paroda/kekdaboard/board/board-left/board-left.kicad_sch

## KiCad design board/board-left/board-left.kicad_sch (2023-03-22)

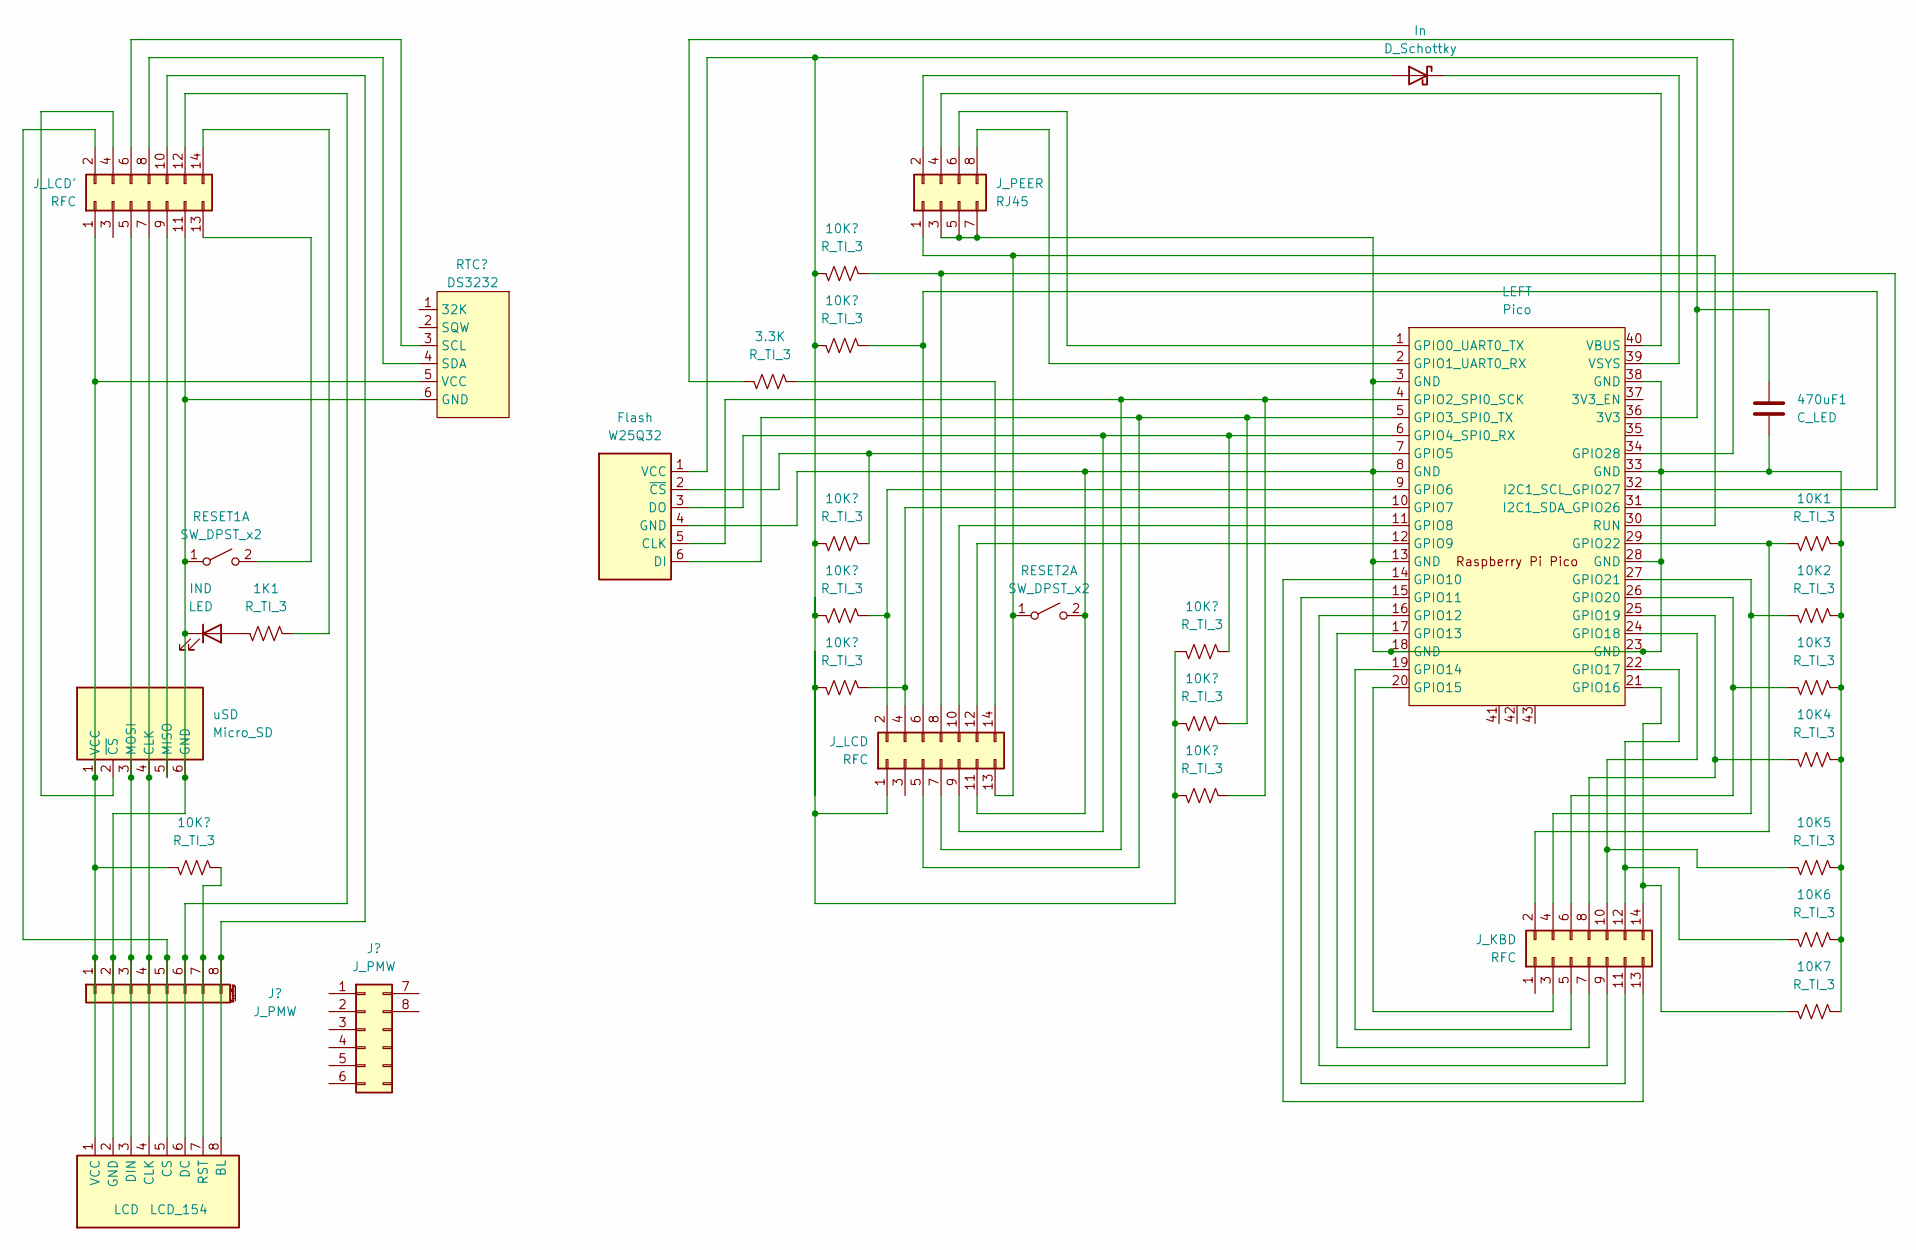
[picture p7: schematic board-left.kicad_sch]

Parts:
1K1, 3.3K, 10K1, 10K2, 10K3, 10K4, 10K5, 10K6, 10K7: R_TI_3; R_Axial_DIN0204_L3.6mm_D1.6mm_P2.54mm_Vertical
470uF1: C_LED
Flash: W25Q32; SOIC-8_5.23x5.23mm_P1.27mm
IND: LED
In: D_Schottky
J_KBD: RFC; PinSocket_2x07_P2.54mm_Vertical
J_LCD: RFC; PinSocket_2x07_P2.54mm_Vertical
J_LCD': RFC; PinSocket_2x07_P2.54mm_Vertical
J_PEER: RJ45; RJ45_Amphenol_54602-x08_Horizontal
LCD: LCD_154; SOIC-8_5.23x5.23mm_P1.27mm
LEFT: Pico; RPi_Pico_SMD_TH
RESET1, RESET2: SW_DPST_x2
uSD: Micro_SD; SOIC-8_5.23x5.23mm_P1.27mm

Connections:
unnamed: 1K1.1, J_LCD'.14
unnamed: 1K1.2, IND.2 (A)
unnamed: 3.3K.1, J_LCD.14
unnamed: 3.3K.2, LEFT.34 (GPIO28)
unnamed: 10K1.1, 10K2.1, 10K3.1, 10K4.1, 10K5.1, 10K6.1, 10K7.1, 470uF1.2, Flash.4 (GND), J_LCD.11, J_PEER.3, J_PEER.5, J_PEER.7, LEFT.3 (GND), LEFT.8 (GND), LEFT.13 (GND), LEFT.18 (GND), LEFT.23 (GND), LEFT.28 (GND), LEFT.33 (GND), LEFT.38 (GND), RESET2.2 (B)
unnamed: 10K1.2, J_KBD.2, LEFT.29 (GPIO22)
unnamed: 10K2.2, J_KBD.4, LEFT.27 (GPIO21)
unnamed: 10K3.2, J_KBD.6, LEFT.26 (GPIO20)
unnamed: 10K4.2, J_KBD.8, LEFT.25 (GPIO19)
unnamed: 10K5.2, J_KBD.10, LEFT.24 (GPIO18)
unnamed: 10K6.2, J_KBD.12, LEFT.22 (GPIO17)
unnamed: 10K7.2, J_KBD.14, LEFT.21 (GPIO16)
unnamed: 470uF1.1, Flash.1 (VCC), J_LCD.1, LEFT.36 (3V3)
unnamed: Flash.2 (~CS), LEFT.7 (GPIO5)
unnamed: Flash.3 (DO), J_LCD.9, LEFT.6 (GPIO4_SPI0_RX)
unnamed: Flash.5 (CLK), J_LCD.7, LEFT.4 (GPIO2_SPI0_SCK)
unnamed: Flash.6 (DI), J_LCD.5, LEFT.5 (GPIO3_SPI0_TX)
unnamed: IND.1 (K), J_LCD'.11, LCD.2 (GND), RESET1.1 (A), uSD.6 (GND)
unnamed: In.1 (K), LEFT.39 (VSYS)
unnamed: In.2 (A), J_PEER.2
unnamed: J_KBD.3, LEFT.20 (GPIO15)
unnamed: J_KBD.5, LEFT.19 (GPIO14)
unnamed: J_KBD.7, LEFT.17 (GPIO13)
unnamed: J_KBD.9, LEFT.16 (GPIO12)
unnamed: J_KBD.11, LEFT.15 (GPIO11)
unnamed: J_KBD.13, LEFT.14 (GPIO10)
unnamed: J_LCD'.1, LCD.1 (VCC), uSD.1 (VCC)
unnamed: J_LCD'.2, LCD.5 (CS)
unnamed: J_LCD'.4, uSD.2 (~CS)
unnamed: J_LCD'.5, LCD.3 (DIN), uSD.3 (MOSI)
unnamed: J_LCD'.7, LCD.4 (CLK), uSD.4 (CLK)
unnamed: J_LCD'.9, uSD.5 (MISO)
unnamed: J_LCD'.10, LCD.8 (BL)
unnamed: J_LCD'.12, LCD.6 (DC)
unnamed: J_LCD'.13, RESET1.2 (B)
unnamed: J_LCD.2, LEFT.9 (GPIO6)
unnamed: J_LCD.4, LEFT.10 (GPIO7)
unnamed: J_LCD.6, LEFT.32 (I2C1_SCL_GPIO27)
unnamed: J_LCD.8, LEFT.31 (I2C1_SDA_GPIO26)
unnamed: J_LCD.10, LEFT.11 (GPIO8)
unnamed: J_LCD.12, LEFT.12 (GPIO9)
unnamed: J_LCD.13, J_PEER.1, LEFT.30 (RUN), RESET2.1 (A)
unnamed: J_PEER.4, LEFT.40 (VBUS)
unnamed: J_PEER.6, LEFT.1 (GPIO0_UART0_TX)
unnamed: J_PEER.8, LEFT.2 (GPIO1_UART0_RX)
