paroda/kekdaboard/picow/hello_bt/gatt_streamer_server.c

/*
 * Copyright (C) 2014 BlueKitchen GmbH
 *
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
 * 1. Redistributions of source code must retain the above copyright
 *    notice, this list of conditions and the following disclaimer.
 * 2. Redistributions in binary form must reproduce the above copyright
 *    notice, this list of conditions and the following disclaimer in the
 *    documentation and/or other materials provided with the distribution.
 * 3. Neither the name of the copyright holders nor the names of
 *    contributors may be used to endorse or promote products derived
 *    from this software without specific prior written permission.
 * 4. Any redistribution, use, or modification is done solely for
 *    personal benefit and not for any commercial purpose or for
 *    monetary gain.
 *
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
 * Please inquire about commercial licensing options at
 * contact@bluekitchen-gmbh.com
 *
 */

#define BTSTACK_FILE__ "gatt_streamer_server.c"

// *****************************************************************************
/* EXAMPLE_START(gatt_streamer_server): Performance - Stream Data over GATT (Server)
 *
 * @text All newer operating systems provide GATT Client functionality.
 * This example shows how to get a maximal throughput via BLE:
 * - send whenever possible,
 * - use the max ATT MTU.
 *
 * @text In theory, we should also update the connection parameters, but we already get
 * a connection interval of 30 ms and there's no public way to use a shorter
 * interval with iOS (if we're not implementing an HID device).
 *
 * @text Note: To start the streaming, run the example.
 * On remote device use some GATT Explorer, e.g. LightBlue, BLExplr to enable notifications.
 */
// *****************************************************************************

#include <inttypes.h>
#include <stdint.h>
#include <stdio.h>
#include <stdlib.h>
#include <string.h>

#include "btstack.h"
#include "pico/cyw43_arch.h"
#include "pico/btstack_cyw43.h"
#include "pico/stdlib.h"

// le_streamer.gatt contains the declaration of the provided GATT Services + Characteristics
// le_streamer.h    contains the binary representation of le_streamer.gatt
// it is generated by the build system by calling: $BTSTACK_ROOT/tool/compile_gatt.py le_streamer.gatt le_streamer.h
// it needs to be regenerated when the GATT Database declared in le_streamer.gatt file is modified
#include "gatt_streamer_server.h"

#define REPORT_INTERVAL_MS 3000
#define MAX_NR_CONNECTIONS 3


static void  hci_packet_handler (uint8_t packet_type, uint16_t channel, uint8_t *packet, uint16_t size);
static void  att_packet_handler (uint8_t packet_type, uint16_t channel, uint8_t *packet, uint16_t size);
static int   att_write_callback(hci_con_handle_t con_handle, uint16_t att_handle, uint16_t transaction_mode, uint16_t offset, uint8_t *buffer, uint16_t buffer_size);
static void  streamer(void);

#define APP_AD_FLAGS 0x06

const uint8_t adv_data[] = {
    // Flags general discoverable
    0x02, BLUETOOTH_DATA_TYPE_FLAGS, APP_AD_FLAGS,
    // Name
    0x0c, BLUETOOTH_DATA_TYPE_COMPLETE_LOCAL_NAME, 'L', 'E', ' ', 'S', 't', 'r', 'e', 'a', 'm', 'e', 'r',
    // Incomplete List of 16-bit Service Class UUIDs -- FF10 - only valid for testing!
    0x03, BLUETOOTH_DATA_TYPE_INCOMPLETE_LIST_OF_16_BIT_SERVICE_CLASS_UUIDS, 0x10, 0xff,
};
const uint8_t adv_data_len = sizeof(adv_data);

static btstack_packet_callback_registration_t hci_event_callback_registration;

// support for multiple clients
typedef struct {
    char name;
    int le_notification_enabled;
    uint16_t value_handle;
    hci_con_handle_t connection_handle;
    int  counter;
    char test_data[200];
    int  test_data_len;
    uint32_t test_data_sent_count;
    uint32_t test_data_sent;
    uint32_t test_data_start;
} le_streamer_connection_t;
static le_streamer_connection_t le_streamer_connections[MAX_NR_CONNECTIONS];

// round robin sending
static int connection_index;

static void init_connections(void){
    // track connections
    int i;
    for (i=0;i<MAX_NR_CONNECTIONS;i++){
        le_streamer_connections[i].connection_handle = HCI_CON_HANDLE_INVALID;
        le_streamer_connections[i].name = 'A' + i;
    }
}

static le_streamer_connection_t * connection_for_conn_handle(hci_con_handle_t conn_handle){
    int i;
    for (i=0;i<MAX_NR_CONNECTIONS;i++){
        if (le_streamer_connections[i].connection_handle == conn_handle) return &le_streamer_connections[i];
    }
    return NULL;
}

static void next_connection_index(void){
    connection_index++;
    if (connection_index == MAX_NR_CONNECTIONS){
        connection_index = 0;
    }
}

/* @section Main Application Setup
 *
 * @text Listing MainConfiguration shows main application code.
 * It initializes L2CAP, the Security Manager, and configures the ATT Server with the pre-compiled
 * ATT Database generated from $le_streamer.gatt$. Finally, it configures the advertisements
 * and boots the Bluetooth stack.
 */

/* LISTING_START(MainConfiguration): Init L2CAP, SM, ATT Server, and enable advertisements */

static void le_streamer_setup(void){

    l2cap_init();

    // setup SM: Display only
    sm_init();

    // setup ATT server
    att_server_init(profile_data, NULL, att_write_callback);

    // register for HCI events
    hci_event_callback_registration.callback = &hci_packet_handler;
    hci_add_event_handler(&hci_event_callback_registration);

    // register for ATT events
    att_server_register_packet_handler(att_packet_handler);

    // setup advertisements
    uint16_t adv_int_min = 0x0030;
    uint16_t adv_int_max = 0x0030;
    uint8_t adv_type = 0;
    bd_addr_t null_addr;
    memset(null_addr, 0, 6);
    gap_advertisements_set_params(adv_int_min, adv_int_max, adv_type, 0, null_addr, 0x07, 0x00);
    gap_advertisements_set_data(adv_data_len, (uint8_t*) adv_data);
    gap_advertisements_enable(1);

    // init client state
    init_connections();
}
/* LISTING_END */

/*
 * @section Track throughput
 * @text We calculate the throughput by setting a start time and measuring the amount of
 * data sent. After a configurable REPORT_INTERVAL_MS, we print the throughput in kB/s
 * and reset the counter and start time.
 */

/* LISTING_START(tracking): Tracking throughput */

static void test_reset(le_streamer_connection_t * context){
    context->test_data_start = btstack_run_loop_get_time_ms();
    context->test_data_sent = 0;
    context->test_data_sent_count = 0;
}

static void test_track_sent(le_streamer_connection_t * context, int bytes_sent){
    context->test_data_sent += bytes_sent;
    context->test_data_sent_count++;

    // evaluate
    uint32_t now = btstack_run_loop_get_time_ms();
    uint32_t time_passed = now - context->test_data_start;
    if (time_passed < REPORT_INTERVAL_MS) return;
    // print speed
    int bytes_per_second = context->test_data_sent * 1000 / time_passed;
    int count_per_second = context->test_data_sent_count * 1000 / time_passed;
    printf("%c: %"PRIu32" bytes sent-> %u.%03u kB/s %u times/sec\n", context->name, context->test_data_sent, bytes_per_second / 1000, bytes_per_second % 1000, count_per_second);

    // restart
    context->test_data_start = now;
    context->test_data_sent  = 0;
    context->test_data_sent_count  = 0;
}
/* LISTING_END(tracking): Tracking throughput */

/*
 * @section HCI Packet Handler
 *
 * @text The packet handler is used track incoming connections and to stop notifications on disconnect
 * It is also a good place to request the connection parameter update as indicated
 * in the commented code block.
 */

/* LISTING_START(hciPacketHandler): Packet Handler */
static void hci_packet_handler (uint8_t packet_type, uint16_t channel, uint8_t *packet, uint16_t size){
    UNUSED(channel);
    UNUSED(size);

    if (packet_type != HCI_EVENT_PACKET) return;

    uint16_t conn_interval;
    hci_con_handle_t con_handle;

    switch (hci_event_packet_get_type(packet)) {
    case BTSTACK_EVENT_STATE:
        // BTstack activated, get started
        if (btstack_event_state_get_state(packet) == HCI_STATE_WORKING) {
            printf("To start the streaming, please run the le_streamer_client example on other device, or use some GATT Explorer, e.g. LightBlue, BLExplr.\n");
        }
        break;
    case HCI_EVENT_DISCONNECTION_COMPLETE:
        con_handle = hci_event_disconnection_complete_get_connection_handle(packet);
        printf("- LE Connection 0x%04x: disconnect, reason %02x\n", con_handle, hci_event_disconnection_complete_get_reason(packet));
        break;
    case HCI_EVENT_LE_META:
        switch (hci_event_le_meta_get_subevent_code(packet)) {
        case HCI_SUBEVENT_LE_CONNECTION_COMPLETE:
            // print connection parameters (without using float operations)
            con_handle    = hci_subevent_le_connection_complete_get_connection_handle(packet);
            conn_interval = hci_subevent_le_connection_complete_get_conn_interval(packet);
            printf("- LE Connection 0x%04x: connected - connection interval %u.%02u ms, latency %u\n", con_handle, conn_interval * 125 / 100,
                   25 * (conn_interval & 3), hci_subevent_le_connection_complete_get_conn_latency(packet));

            // request min con interval 15 ms for iOS 11+
            //printf("- LE Connection 0x%04x: request 15 ms connection interval\n", con_handle);
            //gap_request_connection_parameter_update(con_handle, 12, 12, 4, 0x0048);
            break;
        case HCI_SUBEVENT_LE_CONNECTION_UPDATE_COMPLETE:
            // print connection parameters (without using float operations)
            con_handle    = hci_subevent_le_connection_update_complete_get_connection_handle(packet);
            conn_interval = hci_subevent_le_connection_update_complete_get_conn_interval(packet);
            printf("- LE Connection 0x%04x: connection update - connection interval %u.%02u ms, latency %u\n", con_handle, conn_interval * 125 / 100,
                   25 * (conn_interval & 3), hci_subevent_le_connection_update_complete_get_conn_latency(packet));
            break;
        case HCI_SUBEVENT_LE_DATA_LENGTH_CHANGE:
            con_handle = hci_subevent_le_data_length_change_get_connection_handle(packet);
            printf("- LE Connection 0x%04x: data length change - max %u bytes per packet\n", con_handle,
                   hci_subevent_le_data_length_change_get_max_tx_octets(packet));
            break;
        default:
            break;
        }
        break;

    default:
        break;
    }
}

/* LISTING_END */

/*
 * @section ATT Packet Handler
 *
 * @text The packet handler is used to track the ATT MTU Exchange and trigger ATT send
 */

/* LISTING_START(attPacketHandler): Packet Handler */
static void att_packet_handler (uint8_t packet_type, uint16_t channel, uint8_t *packet, uint16_t size){
    UNUSED(channel);
    UNUSED(size);

    int mtu;
    le_streamer_connection_t * context;
    switch (packet_type) {
    case HCI_EVENT_PACKET:
        switch (hci_event_packet_get_type(packet)) {
        case ATT_EVENT_CONNECTED:
            // setup new
            context = connection_for_conn_handle(HCI_CON_HANDLE_INVALID);
            if (!context) break;
            context->counter = 'A';
            context->connection_handle = att_event_connected_get_handle(packet);
            context->test_data_len = btstack_min(att_server_get_mtu(context->connection_handle) - 3, sizeof(context->test_data));
            printf("%c: ATT connected, handle 0x%04x, test data len %u\n", context->name, context->connection_handle, context->test_data_len);
            break;
        case ATT_EVENT_MTU_EXCHANGE_COMPLETE:
            mtu = att_event_mtu_exchange_complete_get_MTU(packet) - 3;
            context = connection_for_conn_handle(att_event_mtu_exchange_complete_get_handle(packet));
            if (!context) break;
            context->test_data_len = btstack_min(mtu - 3, sizeof(context->test_data));
            printf("%c: ATT MTU = %u => use test data of len %u\n", context->name, mtu, context->test_data_len);
            break;
        case ATT_EVENT_CAN_SEND_NOW:
            streamer();
            break;
        case ATT_EVENT_DISCONNECTED:
            context = connection_for_conn_handle(att_event_disconnected_get_handle(packet));
            if (!context) break;
            // free connection
            printf("%c: ATT disconnected, handle 0x%04x\n", context->name, context->connection_handle);
            context->le_notification_enabled = 0;
            context->connection_handle = HCI_CON_HANDLE_INVALID;
            break;
        default:
            break;
        }
        break;
    default:
        break;
    }
}
/* LISTING_END */

/*
 * @section Streamer
 *
 * @text The streamer function checks if notifications are enabled and if a notification can be sent now.
 * It creates some test data - a single letter that gets increased every time - and tracks the data sent.
 */

/* LISTING_START(streamer): Streaming code */
static void streamer(void){

    // find next active streaming connection
    int old_connection_index = connection_index;
    while (1){
        // active found?
        if ((le_streamer_connections[connection_index].connection_handle != HCI_CON_HANDLE_INVALID) &&
            (le_streamer_connections[connection_index].le_notification_enabled)) break;

        // check next
        next_connection_index();

        // none found
        if (connection_index == old_connection_index) return;
    }

    le_streamer_connection_t * context = &le_streamer_connections[connection_index];

    // create test data
    context->counter++;
    if (context->counter > 'Z') context->counter = 'A';
    memset(context->test_data, context->counter, context->test_data_len);

    // send
    att_server_notify(context->connection_handle, context->value_handle, (uint8_t*) context->test_data, context->test_data_len);

    // track
    test_track_sent(context, context->test_data_len);

    // request next send event
    att_server_request_can_send_now_event(context->connection_handle);

    // check next
    next_connection_index();
}
/* LISTING_END */

/*
 * @section ATT Write
 *
 * @text The only valid ATT write in this example is to the Client Characteristic Configuration, which configures notification
 * and indication. If the ATT handle matches the client configuration handle, the new configuration value is stored.
 * If notifications get enabled, an ATT_EVENT_CAN_SEND_NOW is requested. See Listing attWrite.
 */

/* LISTING_START(attWrite): ATT Write */
static int att_write_callback(hci_con_handle_t con_handle, uint16_t att_handle, uint16_t transaction_mode, uint16_t offset, uint8_t *buffer, uint16_t buffer_size){
    UNUSED(offset);

    // printf("att_write_callback att_handle 0x%04x, transaction mode %u\n", att_handle, transaction_mode);
    if (transaction_mode != ATT_TRANSACTION_MODE_NONE) return 0;
    le_streamer_connection_t * context = connection_for_conn_handle(con_handle);
    switch(att_handle){
    case ATT_CHARACTERISTIC_0000FF11_0000_1000_8000_00805F9B34FB_01_CLIENT_CONFIGURATION_HANDLE:
    case ATT_CHARACTERISTIC_0000FF12_0000_1000_8000_00805F9B34FB_01_CLIENT_CONFIGURATION_HANDLE:
        context->le_notification_enabled = little_endian_read_16(buffer, 0) == GATT_CLIENT_CHARACTERISTICS_CONFIGURATION_NOTIFICATION;
        printf("%c: Notifications enabled %u\n", context->name, context->le_notification_enabled);
        if (context->le_notification_enabled){
            switch (att_handle){
            case ATT_CHARACTERISTIC_0000FF11_0000_1000_8000_00805F9B34FB_01_CLIENT_CONFIGURATION_HANDLE:
                context->value_handle = ATT_CHARACTERISTIC_0000FF11_0000_1000_8000_00805F9B34FB_01_VALUE_HANDLE;
                break;
            case ATT_CHARACTERISTIC_0000FF12_0000_1000_8000_00805F9B34FB_01_CLIENT_CONFIGURATION_HANDLE:
                context->value_handle = ATT_CHARACTERISTIC_0000FF12_0000_1000_8000_00805F9B34FB_01_VALUE_HANDLE;
                break;
            default:
                break;
            }
            att_server_request_can_send_now_event(context->connection_handle);
        }
        test_reset(context);
        break;
    case ATT_CHARACTERISTIC_0000FF11_0000_1000_8000_00805F9B34FB_01_VALUE_HANDLE:
    case ATT_CHARACTERISTIC_0000FF12_0000_1000_8000_00805F9B34FB_01_VALUE_HANDLE:
        test_track_sent(context, buffer_size);
        break;
    default:
        printf("Write to 0x%04x, len %u\n", att_handle, buffer_size);
        break;
    }
    return 0;
}
/* LISTING_END */

int btstack_main(void);
int btstack_main(void)
{
    le_streamer_setup();

    // turn on!
    hci_power_control(HCI_POWER_ON);

    return 0;
}
/* EXAMPLE_END */



int main() {

    stdio_init_all();
    sleep_ms(2000);

    printf("Booting up streamer\n");


    // initialize CYW43 driver architecture (will enable BT if/because CYW43_ENABLE_BLUETOOTH == 1)
    if (cyw43_arch_init()) {
        printf("failed to initialise cyw43_arch\n");
        printf("abort!\n");
        sleep_ms(2000);
    }

    printf("cyw43 inited\n");

    cyw43_arch_gpio_put(CYW43_WL_GPIO_LED_PIN, 1);

    btstack_main();

    // btstack_run_loop_execute is only required when using the 'polling' method (e.g. using pico_cyw43_arch_poll library).
    // btstack_run_loop_execute();

    while(true) {
        cyw43_arch_gpio_put(CYW43_WL_GPIO_LED_PIN, 1);
        sleep_ms(300);
        cyw43_arch_gpio_put(CYW43_WL_GPIO_LED_PIN, 0);
        sleep_ms(300);
    }

    return 0;
}
