paroda/kekdaboard/pico/hello_pwm/hello_pwm.c

/**
 * Copyright (c) 2020 Raspberry Pi (Trading) Ltd.
 *
 * SPDX-License-Identifier: BSD-3-Clause
 */

// Output PWM signals on pins 0 and 1

#include "pico/stdlib.h"
#include "hardware/pwm.h"

int main() {
    /// \tag::setup_pwm[]

    // Tell GPIO 0 and 1 they are allocated to the PWM
    gpio_set_function(0, GPIO_FUNC_PWM);
    gpio_set_function(1, GPIO_FUNC_PWM);

    // Find out which PWM slice is connected to GPIO 0 (it's slice 0)
    // uint slice_num = pwm_gpio_to_slice_num(0);
    uint slice_num = pwm_gpio_to_slice_num(1);

    // 50Hz - 38,0
    // 100Hz - 19,0
    pwm_set_clkdiv_int_frac(slice_num, 2, 0);
    pwm_set_wrap(slice_num, 65535);
    pwm_set_chan_level(slice_num, PWM_CHAN_B, 7*65535/10);
    
    // Set the PWM running
    pwm_set_enabled(slice_num, true);
    /// \end::setup_pwm[]

    // Note we could also use pwm_set_gpio_level(gpio, x) which looks up the
    // correct slice and channel for a given GPIO.
}
