paroda/kekdaboard/pico/kbd/srom_pmw3389.c

#include <pico/platform.h>

#include "srom_pmw3389.h"

// Firmware "ORCA3_ROW_SROMxE8"

const unsigned short firmware_length = 4094;

const unsigned char __in_flash() firmware_data[] = {
0x01, 0xe8, 0xba, 0x26, 0x0b, 0xb2, 0xbe, 0xfe, 0x7e, 0x5f, 0x3c, 0xdb, 0x15, 0xa8, 0xb3,
0xe4, 0x2b, 0xb5, 0xe8, 0x53, 0x07, 0x6d, 0x3b, 0xd1, 0x20, 0xc2, 0x06, 0x6f, 0x3d, 0xd9,
0x11, 0xa0, 0xc2, 0xe7, 0x2d, 0xb9, 0xd1, 0x20, 0xa3, 0xa5, 0xc8, 0xf3, 0x64, 0x4a, 0xf7,
0x4d, 0x18, 0x93, 0xa4, 0xca, 0xf7, 0x6c, 0x5a, 0x36, 0xee, 0x5e, 0x3e, 0xfe, 0x7e, 0x7e,
0x5f, 0x1d, 0x99, 0xb0, 0xc3, 0xe5, 0x29, 0xd3, 0x03, 0x65, 0x48, 0x12, 0x87, 0x6d, 0x58,
0x32, 0xe6, 0x2f, 0xdc, 0x3a, 0xf2, 0x4f, 0xfd, 0x59, 0x11, 0x81, 0x61, 0x21, 0xc0, 0x02,
0x86, 0x8e, 0x7f, 0x5d, 0x38, 0xf2, 0x47, 0x0c, 0x7b, 0x55, 0x28, 0xb3, 0xe4, 0x4a, 0x16,
0xab, 0xbf, 0xdd, 0x38, 0xf2, 0x66, 0x4e, 0xff, 0x5d, 0x19, 0x91, 0xa0, 0xa3, 0xa5, 0xc8,
0x12, 0xa6, 0xaf, 0xdc, 0x3a, 0xd1, 0x41, 0x60, 0x75, 0x58, 0x24, 0x92, 0xd4, 0x72, 0x6c,
0xe0, 0x2f, 0xfd, 0x23, 0x8d, 0x1c, 0x5b, 0xb2, 0x97, 0x36, 0x3d, 0x0b, 0xa2, 0x49, 0xb1,
0x58, 0xf2, 0x1f, 0xc0, 0xcb, 0xf8, 0x41, 0x4f, 0xcd, 0x1e, 0x6b, 0x39, 0xa7, 0x2b, 0xe9,
0x30, 0x16, 0x83, 0xd2, 0x0e, 0x47, 0x8f, 0xe3, 0xb1, 0xdf, 0xa2, 0x15, 0xdb, 0x5d, 0x30,
0xc5, 0x1a, 0xab, 0x31, 0x99, 0xf3, 0xfa, 0xb2, 0x86, 0x69, 0xad, 0x7a, 0xe8, 0xa7, 0x18,
0x6a, 0xcc, 0xc8, 0x65, 0x23, 0x87, 0xa8, 0x5f, 0xf5, 0x21, 0x59, 0x75, 0x09, 0x71, 0x45,
0x55, 0x25, 0x4b, 0xda, 0xa1, 0xc3, 0xf7, 0x41, 0xab, 0x59, 0xd9, 0x74, 0x12, 0x55, 0x5f,
0xbc, 0xaf, 0xd9, 0xfd, 0xb0, 0x1e, 0xa3, 0x0f, 0xff, 0xde, 0x11, 0x16, 0x6a, 0xae, 0x0e,
0xe1, 0x5d, 0x3c, 0x10, 0x43, 0x9a, 0xa1, 0x0b, 0x24, 0x8f, 0x0d, 0x7f, 0x0b, 0x5e, 0x4c,
0x42, 0xa4, 0x84, 0x2c, 0x40, 0xd0, 0x55, 0x39, 0xe6, 0x4b, 0xf8, 0x9b, 0x2f, 0xdc, 0x28,
0xff, 0xfa, 0xb5, 0x85, 0x19, 0xe5, 0x28, 0xa1, 0x77, 0xaa, 0x73, 0xf3, 0x03, 0xc7, 0x62,
0xa6, 0x91, 0x18, 0xc9, 0xb0, 0xcd, 0x05, 0xdc, 0xca, 0x81, 0x26, 0x1a, 0x47, 0x40, 0xda,
0x36, 0x7d, 0x6a, 0x53, 0xc8, 0x5a, 0x77, 0x5d, 0x19, 0xa4, 0x1b, 0x23, 0x83, 0xd0, 0xb2,
0xaa, 0x0e, 0xbf, 0x77, 0x4e, 0x3a, 0x3b, 0x59, 0x00, 0x31, 0x0d, 0x02, 0x1b, 0x88, 0x7a,
0xd4, 0xbd, 0x9d, 0xcc, 0x58, 0x04, 0x69, 0xf6, 0x3b, 0xca, 0x42, 0xe2, 0xfd, 0xc3, 0x3d,
0x39, 0xc5, 0xd0, 0x71, 0xe4, 0xc8, 0xb7, 0x3e, 0x3f, 0xc8, 0xe9, 0xca, 0xc9, 0x3f, 0x04,
0x4e, 0x1b, 0x79, 0xca, 0xa5, 0x61, 0xc2, 0xed, 0x1d, 0xa6, 0xda, 0x5a, 0xe9, 0x7f, 0x65,
0x8c, 0xbe, 0x12, 0x6e, 0xa4, 0x5b, 0x33, 0x2f, 0x84, 0x28, 0x9c, 0x1c, 0x88, 0x2d, 0xff,
0x07, 0xbf, 0xa6, 0xd7, 0x5a, 0x88, 0x86, 0xb0, 0x3f, 0xf6, 0x31, 0x5b, 0x11, 0x6d, 0xf5,
0x58, 0xeb, 0x58, 0x02, 0x9e, 0xb5, 0x9a, 0xb1, 0xff, 0x25, 0x9d, 0x8b, 0x4f, 0xb6, 0x0a,
0xf9, 0xea, 0x3e, 0x3f, 0x21, 0x09, 0x65, 0x21, 0x22, 0xfe, 0x3d, 0x4e, 0x11, 0x5b, 0x9e,
0x5a, 0x59, 0x8b, 0xdd, 0xd8, 0xce, 0xd6, 0xd9, 0x59, 0xd2, 0x1e, 0xfd, 0xef, 0x0d, 0x1b,
0xd9, 0x61, 0x7f, 0xd7, 0x2d, 0xad, 0x62, 0x09, 0xe5, 0x22, 0x63, 0xea, 0xc7, 0x31, 0xd9,
0xa1, 0x38, 0x80, 0x5c, 0xa7, 0x32, 0x82, 0xec, 0x1b, 0xa2, 0x49, 0x5a, 0x06, 0xd2, 0x7c,
0xc9, 0x96, 0x57, 0xbb, 0x17, 0x75, 0xfc, 0x7a, 0x8f, 0x0d, 0x77, 0xb5, 0x7a, 0x8e, 0x3e,
0xf4, 0xba, 0x2f, 0x69, 0x13, 0x26, 0xd6, 0xd9, 0x21, 0x60, 0x2f, 0x21, 0x3e, 0x87, 0xee,
0xfd, 0x87, 0x16, 0x0d, 0xc8, 0x08, 0x00, 0x25, 0x71, 0xac, 0x2c, 0x03, 0x2a, 0x37, 0x2d,
0xb3, 0x34, 0x09, 0x91, 0xe3, 0x06, 0x2c, 0x38, 0x37, 0x95, 0x3b, 0x17, 0x7a, 0xaf, 0xac,
0x99, 0x55, 0xab, 0x41, 0x39, 0x5f, 0x8e, 0xa6, 0x43, 0x80, 0x03, 0x88, 0x6f, 0x7d, 0xbd,
0x5a, 0xb4, 0x2b, 0x32, 0x23, 0x5a, 0xa9, 0x31, 0x32, 0x39, 0x4c, 0x5b, 0xf4, 0x6b, 0xaf,
0x66, 0x6f, 0x3c, 0x8e, 0x2d, 0x82, 0x97, 0x9f, 0x4a, 0x01, 0xdc, 0x99, 0x98, 0x00, 0xec,
0x38, 0x7a, 0x79, 0x70, 0xa6, 0x85, 0xd6, 0x21, 0x63, 0x0d, 0x45, 0x9a, 0x2e, 0x5e, 0xa7,
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
