paroda/kekdaboard/pico/kbd/lcd_fonts.c

#include <pico/platform.h>

#include "lcd_fonts.h"

// Courier New

const uint8_t __in_flash() Font8_Table[] = {
	// @0 ' ' (5 pixels wide)
	0x00, //
	0x00, //
	0x00, //
	0x00, //
	0x00, //
	0x00, //
	0x00, //
	0x00, //

	// @8 '!' (5 pixels wide)
	0x20, //   #
	0x20, //   #
	0x20, //   #
	0x20, //   #
	0x00, //
	0x20, //   #
	0x00, //
	0x00, //

	// @16 '"' (5 pixels wide)
	0x50, //  # #
	0x50, //  # #
	0x00, //
	0x00, //
	0x00, //
	0x00, //
	0x00, //
	0x00, //

	// @24 '#' (5 pixels wide)
	0x28, //   # #
	0x50, //  # #
	0xF8, // #####
	0x50, //  # #
	0xF8, // #####
	0x50, //  # #
	0xA0, // # #
	0x00, //

	// @32 '$' (5 pixels wide)
	0x20, //   #
	0x30, //   ##
	0x60, //  ##
	0x30, //   ##
	0x10, //    #
	0x60, //  ##
	0x20, //   #
	0x00, //

	// @40 '%' (5 pixels wide)
	0x20, //   #
	0x20, //   #
	0x18, //    ##
	0x60, //  ##
	0x10, //    #
	0x10, //    #
	0x00, //
	0x00, //

	// @48 '&' (5 pixels wide)
	0x00, //
	0x38, //   ###
	0x20, //   #
	0x60, //  ##
	0x50, //  # #
	0x78, //  ####
	0x00, //
	0x00, //

	// @56 ''' (5 pixels wide)
	0x20, //   #
	0x20, //   #
	0x20, //   #
	0x00, //
	0x00, //
	0x00, //
	0x00, //
	0x00, //

	// @64 '(' (5 pixels wide)
	0x10, //    #
	0x20, //   #
	0x20, //   #
	0x20, //   #
	0x20, //   #
	0x20, //   #
	0x10, //    #
	0x00, //

	// @72 ')' (5 pixels wide)
	0x40, //  #
	0x20, //   #
	0x20, //   #
	0x20, //   #
	0x20, //   #
	0x20, //   #
	0x40, //  #
	0x00, //

	// @80 '*' (5 pixels wide)
	0x20, //   #
	0x70, //  ###
	0x20, //   #
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
	0x01, 0x80, 0x00, //        ##
	0x01, 0x80, 0x00, //        ##
	0x01, 0x80, 0x00, //        ##
	0x01, 0x80, 0x00, //        ##
	0x07, 0x80, 0x00, //      ####
	0x07, 0x00, 0x00, //      ###
	0x00, 0x00, 0x00, //
	0x00, 0x00, 0x00, //
	0x00, 0x00, 0x00, //
	0x00, 0x00, 0x00, //

	// @6768 '~' (17 pixels wide)
	0x00, 0x00, 0x00, //
	0x00, 0x00, 0x00, //
	0x00, 0x00, 0x00, //
	0x00, 0x00, 0x00, //
	0x00, 0x00, 0x00, //
	0x00, 0x00, 0x00, //
	0x00, 0x00, 0x00, //
	0x00, 0x00, 0x00, //
	0x0E, 0x00, 0x00, //     ###
	0x1F, 0x18, 0x00, //    #####   ##
	0x3B, 0xB8, 0x00, //   ### ### ###
	0x31, 0xF0, 0x00, //   ##   #####
	0x00, 0xE0, 0x00, //         ###
	0x00, 0x00, 0x00, //
	0x00, 0x00, 0x00, //
	0x00, 0x00, 0x00, //
	0x00, 0x00, 0x00, //
	0x00, 0x00, 0x00, //
	0x00, 0x00, 0x00, //
	0x00, 0x00, 0x00, //
	0x00, 0x00, 0x00, //
	0x00, 0x00, 0x00, //
	0x00, 0x00, 0x00, //
	0x00, 0x00, 0x00, //
};

lcd_font_t lcd_font24 = {
    Font24_Table,
    17, // width
    24, // height
    72  // size 3x24
};
